OscarBazylewich/Phaser_and_Overdrive_Custom_Guitar_Pedal/LTSpice/Schematic.asc

B1: voltage; V=V(Input)/10
C1: cap; 1�
C2: cap; 4.7�
C3: cap; 82p
C4: cap; 22n
C5: cap; 22n
C6: cap; 22n
C7: cap; 22n
C8: cap; 1�
C9: cap; 82p
C10: cap; 22n
C11: cap; 22n
C12: cap; 1�
C13: cap; 22n
D1: diode; 1N4007
D2: diode; 1N4007
D3: diode; 1N4007
D4: diode; 1N4007
Pot1-Linear: potentiometer; Rtot=1Meg wiper=1
Pot2-Linear: potentiometer; Rtot=220k wiper=0.6
Pot3-Linear: potentiometer; Rtot=500k wiper=0.5
Pot4-Linear: potentiometer; Rtot=1Meg wiper=1
Pot5-Log: potentiometer; Rtot=1Meg wiper=1
Pot6-Linear: potentiometer; Rtot=1Meg wiper=1
Q1: njf; J113
Q2: njf; J113
Q3: njf; J113
Q4: njf; J113
R1: res; 1Meg
R2: res; 56k
R3: res; 20k
R4: res; 56k
R5: res; 56k
R6: res; 56k
R7: res; 56k
R8: res; 56k
R9: res; 56k
R10: res; 56k
R11: res; 56k
R12: res; 56k
R13: res; 56k
R14: res; 56k
R15: res; 56k
R16: res; 56k
R17: res; 56k
R18: res; 56k
R19: res; 56k
R20: res; 1Meg
R21: res; 10k
R22: res; 56k
R23: res; 10k
R24: res; 2.2k
R25: res; 10k
R26: res; 1Meg
U1: TL072
U2: TL072
U3: TL072
U4: TL072
U5: TL072
U6: TL072
U7: TL072
U8: TL072
U9: TL072
U10: TL072
U11: TL072
V1: voltage; 4.5; Rser=15
V2: voltage; -4.5; Rser=15
V3: voltage; SINE(0 1 100); AC 1; Rser=10k
Named nets: 0, +V, -V, Input, TriangleOut, SignalOutPhaser, SignalSource, InputSignal, SquareOut, SignalOutOD
Circuit will have 6V-18V fed into a 
Buck converter, voltage inverters, and LDOs to create a dual supply
Power Supply and Input Signal
.tran 0 15s 0s startup
.inc potentiometer.sub
.ac dec 67 20 200000
.step param S 0.3 0.6 0.1
.wave "C:\\Users\\OscarTUF-A16\\Downloads\\GuitarChordsPhaser.wav" 16 44.1k V(SignalOutPhaser)
wavefile="GuitarFChordIn.wav"
Note: Resistors utilized will be E96 series (+-1% Tolerance)
wavefile="GuitarChords.wav"
.wave "C:\\Users\\OscarTUF-A16\\Downloads\\GuitarChordsOD.wav" 16 44.1k V(SignalOutOD)
Note: All Pots here function linearly but will be replaced with its name when assembled
Audio Output
Phase Shifter
Signal Adder
Raw Signal
Phased Signal
Design inspired by MXR Phase 90
Phase Shifter Causes 2 Downward Notches to appear at:
f_1 = [tan(45/2)]/(2*pi*R*C) = 53.510 Hz
f_2 = [tan(135/2)]/(2*pi*R*C) = 311.878 Hz
R
C
Min = -0.5V
Max = -3.0V
Buffer
Overdrive
Min Gain -> 34.659 KHz
Max Gain -> 1.837 KHz
Audio Input
Audio Output
Design Inspired by BOSS OD-1 and Ibanez Tube Screamer
Passive Low Pass Filter 
f = 723.431 Hz
Active High Pass Filter
Wiper = 1, f = 3.288 kHz
Wiper = 0, f = 70.785 Hz
Buffer and AC Coupling
f = 1/(2*ln(1 + (2*R2) / Pot2)*(R3+Pot1)*C2)
Frequency of LFO
Gain = 1+ R2/Pot2
wavefile="Guitar.wav"
DC Offset
J113 V_GS cutoff
Triangle Wave
Min = -0.08V
Max = -1.85V
Depth
Triangle LFO
Min Gain: 5.6x
Max Gain: 105.6x
Low Pass Filter at:
Pot 3 Wiper at 0.3:
Min f = 0.185 Hz
Max f = 12.205 Hz
Gain: 2
Pot 2 Wiper at 0.49:
Amplitude = 1.77V
